zookzook/Slide-Bar/code/Bar/mode_1.cpp

#include "types.h"
#include "input.h"

void enter_mode_1(void) {
  set_pwm();
}

void run_mode_1(void) {
  
  int n = get_value();
  int i = 0;
  while(i < MAX_BARS) {

    LED* result = &LEDS[i];
    if( i <= n ) {
      result->current = 255;      
    } // if 
    else {
      result->current = 0;
    } // else 
    i++;
  }

}
