zookzook/Slide-Bar/code/Bar/mode_1.h

#ifndef _MODE_1_H
#define _MODE_1_H

/**
 * mode 1:
 * 
 * Standard slider mode: The value is displayed from bottom to top with the LEDs switched on.
 */
void run_mode_1(void);
void enter_mode_1(void);

#endif
